PowerPlane/insert-coin/variants/business-card-v1/firmware/production-pond/src/pins.h

// Pin map for business-card-v1 (ATtiny1616 VQFN-20).
// Production copy of bringup/src/pins.h -- verified against
// hardware/production/netlist.ipc. Keep these two in sync until they get
// hoisted into insert-coin/shared/firmware/.

#pragma once

#include <Arduino.h>

#define NUM_BANKS 9

// LED cathode-bank gate drivers (active high; gate HIGH -> bank lit).
// Each "bank" sinks the cathodes of a fixed group of LEDs to GND.
//
//   Bank 0  PA1  D1, D2          (Q1)   ducky frame 1 (boot capture)
//   Bank 1  PA2  D3, D4          (Q2)   ducky frame 2
//   Bank 2  PA3  D5, D6          (Q3)   ducky frame 3
//   Bank 3  PA4  D7, D8          (Q4)   ducky frame 4
//   Bank 4  PA5  D9..D12         (Q5)   great luck     (4 LEDs)
//   Bank 5  PA6  D13..D16        (Q7)   little luck    (4 LEDs)
//   Bank 6  PA7  D17..D20        (Q8)   uncertain luck (4 LEDs)
//   Bank 7  PB2  D21, D22        (Q9)   bad luck -- fire ORANGE
//   Bank 8  PB3  D23, D24        (Q10)  bad luck -- fire RED
//
// Individual-LED addressing is not possible: all 24 anodes go through
// individual current-limit resistors to VCC, so an LED is lit whenever
// its bank's MOSFET is on.
constexpr uint8_t LED_BANK_PINS[NUM_BANKS] = {
    PIN_PA1, PIN_PA2, PIN_PA3, PIN_PA4, PIN_PA5,
    PIN_PA6, PIN_PA7, PIN_PB2, PIN_PB3,
};

// Semantic indices used by the animation script.
constexpr uint8_t BANK_DUCKY_FRAME_1 = 0;
constexpr uint8_t BANK_DUCKY_FRAME_2 = 1;
constexpr uint8_t BANK_DUCKY_FRAME_3 = 2;
constexpr uint8_t BANK_DUCKY_FRAME_4 = 3;
constexpr uint8_t BANK_GREAT_LUCK    = 4;
constexpr uint8_t BANK_LITTLE_LUCK   = 5;
constexpr uint8_t BANK_UNCERTAIN     = 6;
constexpr uint8_t BANK_FIRE_ORANGE   = 7;
constexpr uint8_t BANK_FIRE_RED      = 8;

// Fortune indices returned by the lottery. Match the reveal dispatch
// order in anim_run_reveal().
constexpr uint8_t FORTUNE_GREAT     = 0;
constexpr uint8_t FORTUNE_LITTLE    = 1;
constexpr uint8_t FORTUNE_UNCERTAIN = 2;
constexpr uint8_t FORTUNE_BAD       = 3;
constexpr uint8_t FORTUNE_COUNT     = 4;

// Microphone analog input.
// On the ATtiny1616 txy6 pin map, PC0 is ADC1 AIN6 -- NOT ADC0 AIN6
// (ADC0 AIN6 is PA6, which is LED bank 5). Sampling ADC0 here would
// read the LED gate, not the mic.
#define MIC_PIN          PIN_PC0
#define MIC_ADC          ADC1
#define MIC_ADC_MUXPOS   ADC_MUXPOS_AIN6_gc

// I2C bus to ST25DV04K NFC tag (default TWI pins).
//   PB0 = SCL
//   PB1 = SDA
// Production firmware does NOT initialize I2C -- the tag is RF-powered
// for tap-to-URL, independent of the MCU. Listed here for completeness.
#define ST25DV_I2C_ADDR_USER   0x53
#define ST25DV_I2C_ADDR_SYSTEM 0x57

// Pins broken out from the MCU but not wired to anything on the PCB.
// Disable their input buffers to keep sleep leakage down.
//   PB4 -- /LED10 net stub: out of MCU but nothing on the other end
//   PB5 -- no connect
//   PC1, PC2, PC3 -- no connect
constexpr uint8_t UNUSED_PINS[] = {
    PIN_PB4, PIN_PB5, PIN_PC1, PIN_PC2, PIN_PC3,
};
constexpr uint8_t NUM_UNUSED_PINS = sizeof(UNUSED_PINS) / sizeof(UNUSED_PINS[0]);
