PowerPlane/insert-coin/variants/business-card-v1/firmware/production-pond/src/anim.h

// Scripted animations for the fortune-telling sequence.
//
// Run them in order from setup(): boot_capture -> ducky_walk -> lottery
// -> run_reveal(lottery_result). Each function is blocking; the entire
// show is a single forward pass with no loops at this layer.

#pragma once

#include <stdint.h>

// Bank 0 ramps up, dips, recovers, holds at full. Ends with bank 0 lit.
void anim_boot_capture();

// Stop-motion left-to-right across banks 0..3 with eased dwell.
// Ends with everything off.
void anim_ducky_walk();

// Slot-machine spin across banks 4, 5, 6, 7+8 with accelerating-then-
// decelerating dwell. Re-seeds the RNG from a fresh mic burst at the
// end and returns the chosen fortune index (0 = great, 1 = little,
// 2 = uncertain, 3 = bad).
uint8_t anim_lottery();

// Dispatch to the per-fortune reveal animation.
void anim_run_reveal(uint8_t fortune);

// The card has entered setup mode: one sweep DOWN the strip, from the
// bad-luck banks to the first ducky frame.
//
// Backwards on purpose. Every other animation on this card runs forwards —
// the duck walks left to right, the lottery climbs, the reveals bloom — so
// a single reverse sweep is the one motion that cannot be mistaken for
// part of the game. It says "this is not a turn" without a word.
void anim_setup_enter();

// Setup mode is over: the same sweep, forwards, first ducky to the
// bad-luck banks. The mirror of the way in, so leaving cannot be confused
// with arriving — which it would be if both played the same animation.
void anim_setup_leave();

// The gesture landed but the tag could not be written. Same shape as the
// armed sweep and the opposite direction, because a keeper standing there
// needs to know the difference before they reach for their phone.
void anim_claim_failed();
